xoob/parametric-picture-frame/previews/clips_iso.png

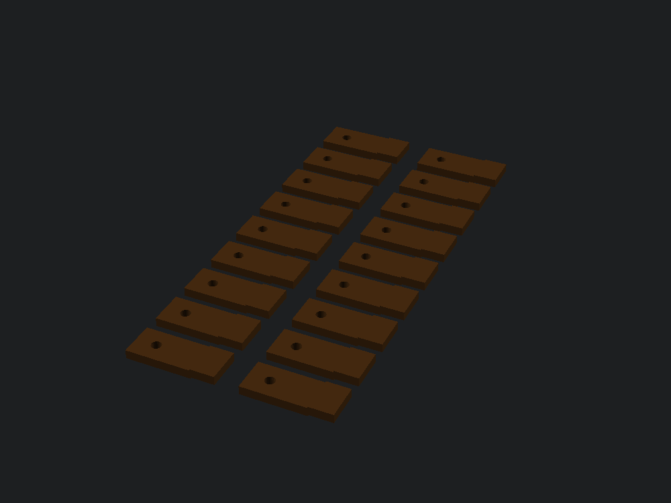
previews/clips_iso.png
