xoob/parametric-picture-frame/previews/f3d_full.png

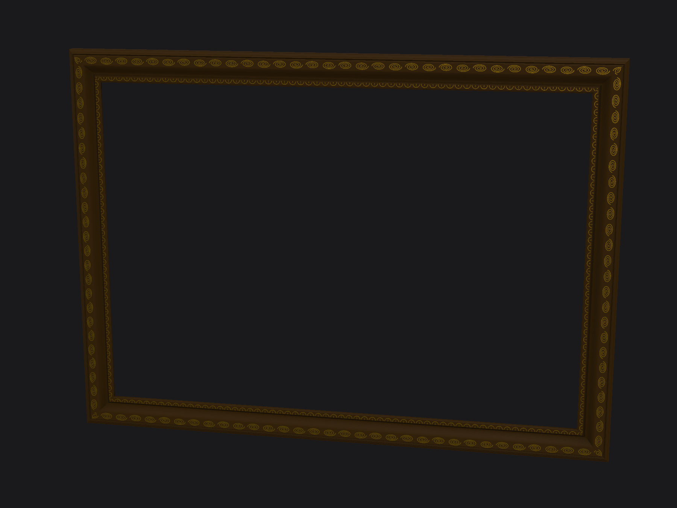
previews/f3d_full.png
