xoob/parametric-picture-frame/previews/fit_iso.png

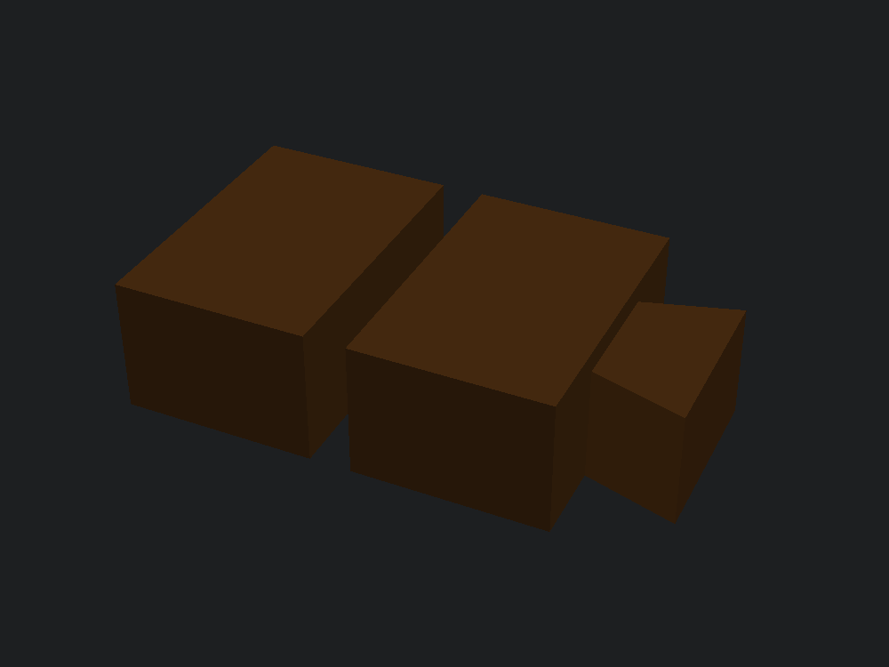
previews/fit_iso.png
