xoob/parametric-picture-frame/previews/hd/clips_iso.png

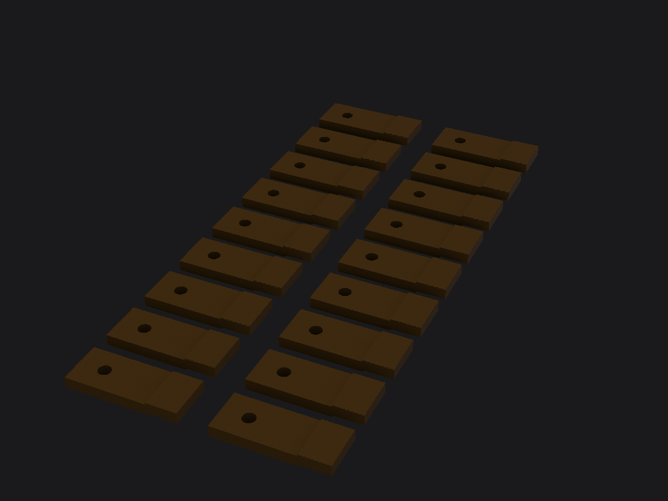
previews/hd/clips_iso.png
