xoob/parametric-picture-frame/previews/hd/corner_bl_back.png

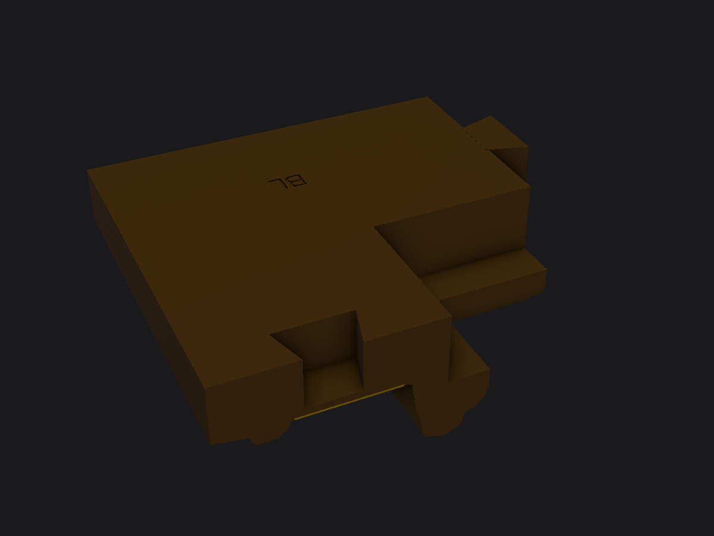
previews/hd/corner_bl_back.png
