xoob/parametric-picture-frame/previews/hd/corner_bl_iso.png

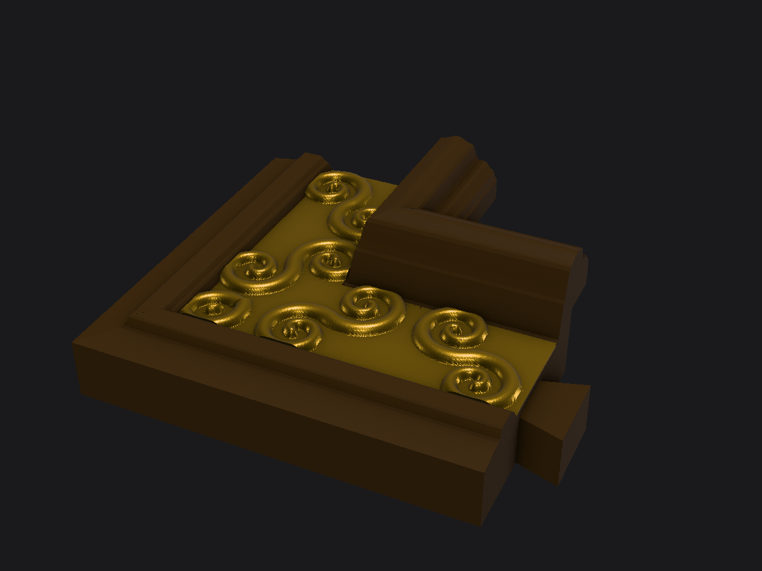
previews/hd/corner_bl_iso.png
