xoob/parametric-picture-frame/previews/hd/exploded_iso.png

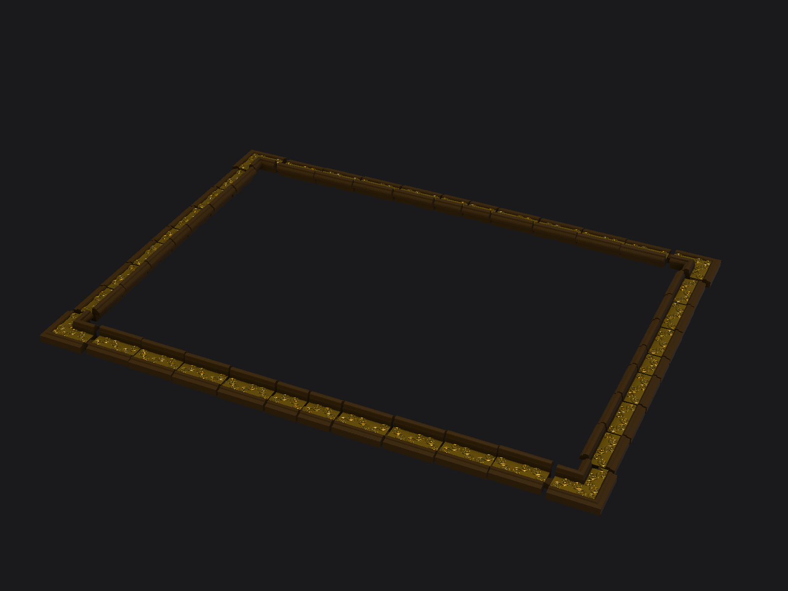
previews/hd/exploded_iso.png
