xoob/parametric-picture-frame/previews/hd/part_b2_iso.png

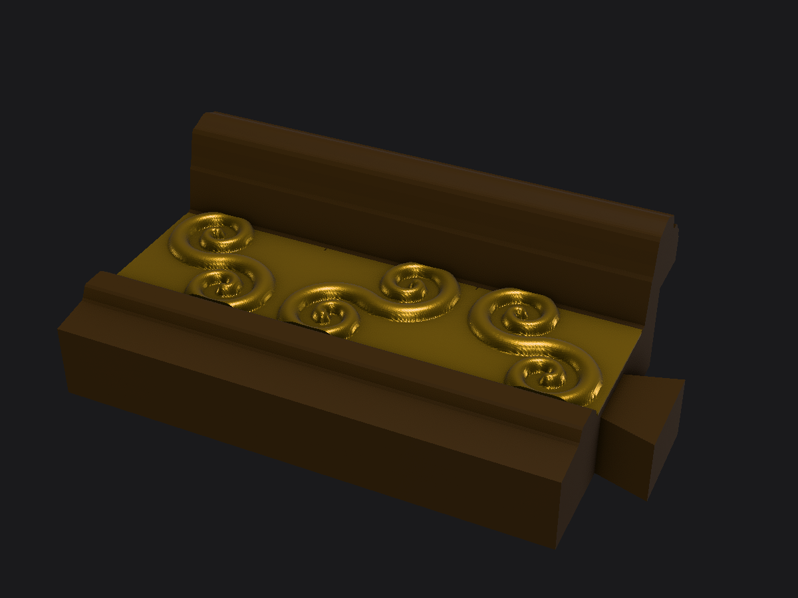
previews/hd/part_b2_iso.png
