xoob/parametric-picture-frame/previews/hd/style_ripple.png

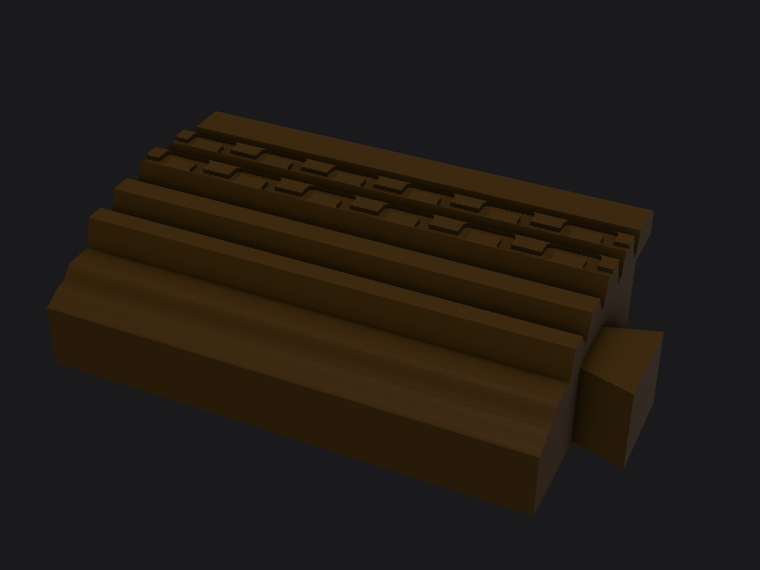
previews/hd/style_ripple.png
