xoob/parametric-picture-frame/previews/part_b2_iso.png

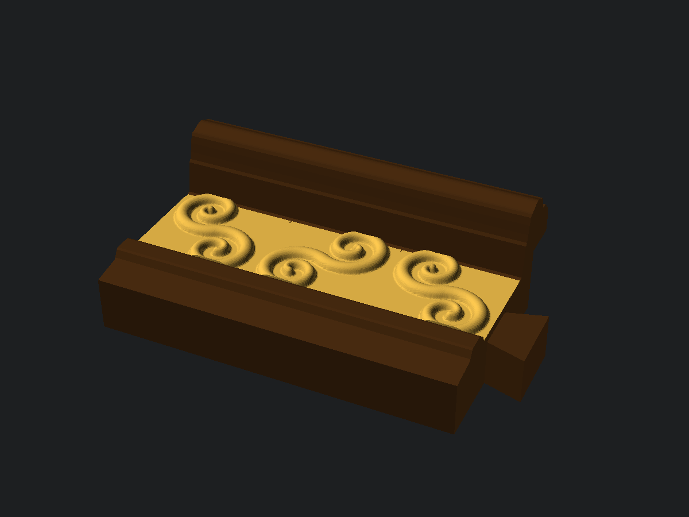
previews/part_b2_iso.png
