xoob/parametric-picture-frame/previews/part_b2_right.png

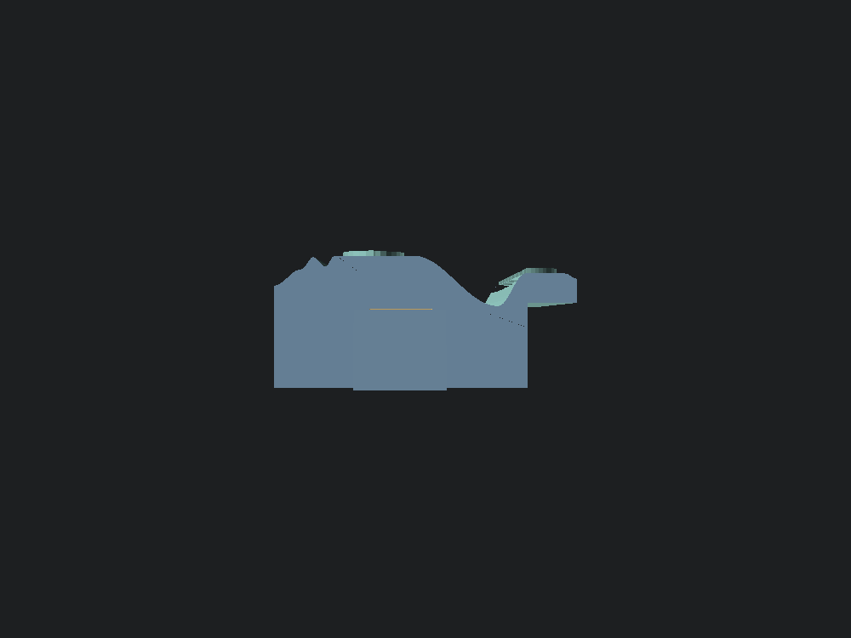
previews/part_b2_right.png
