xoob/parametric-picture-frame/previews/style_revogee.png

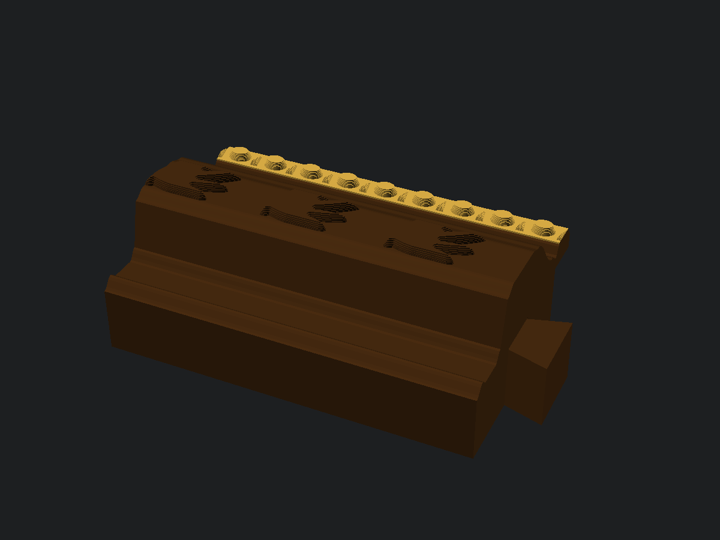
previews/style_revogee.png
