xoob/parametric-picture-frame/previews/assembled_top.png

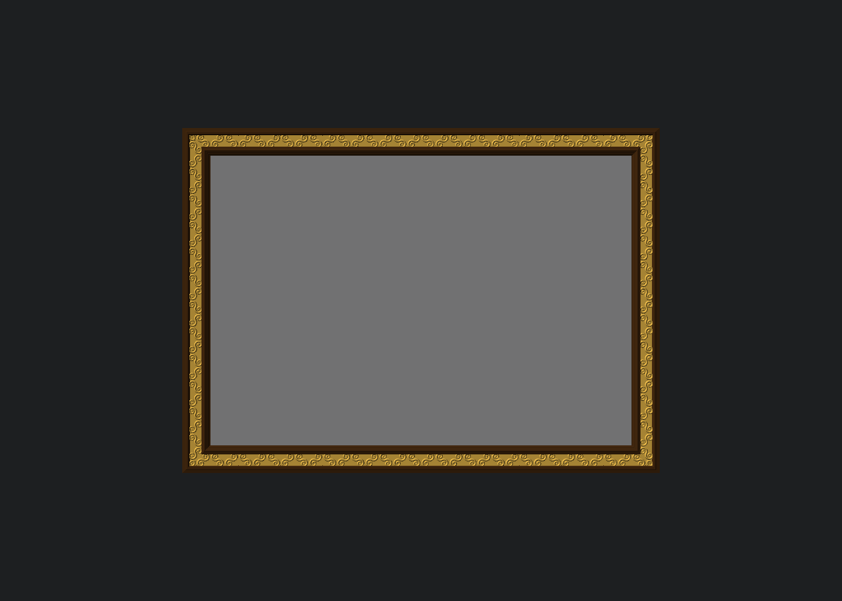
previews/assembled_top.png
