xoob/parametric-picture-frame/previews/hd/assembled_top.png

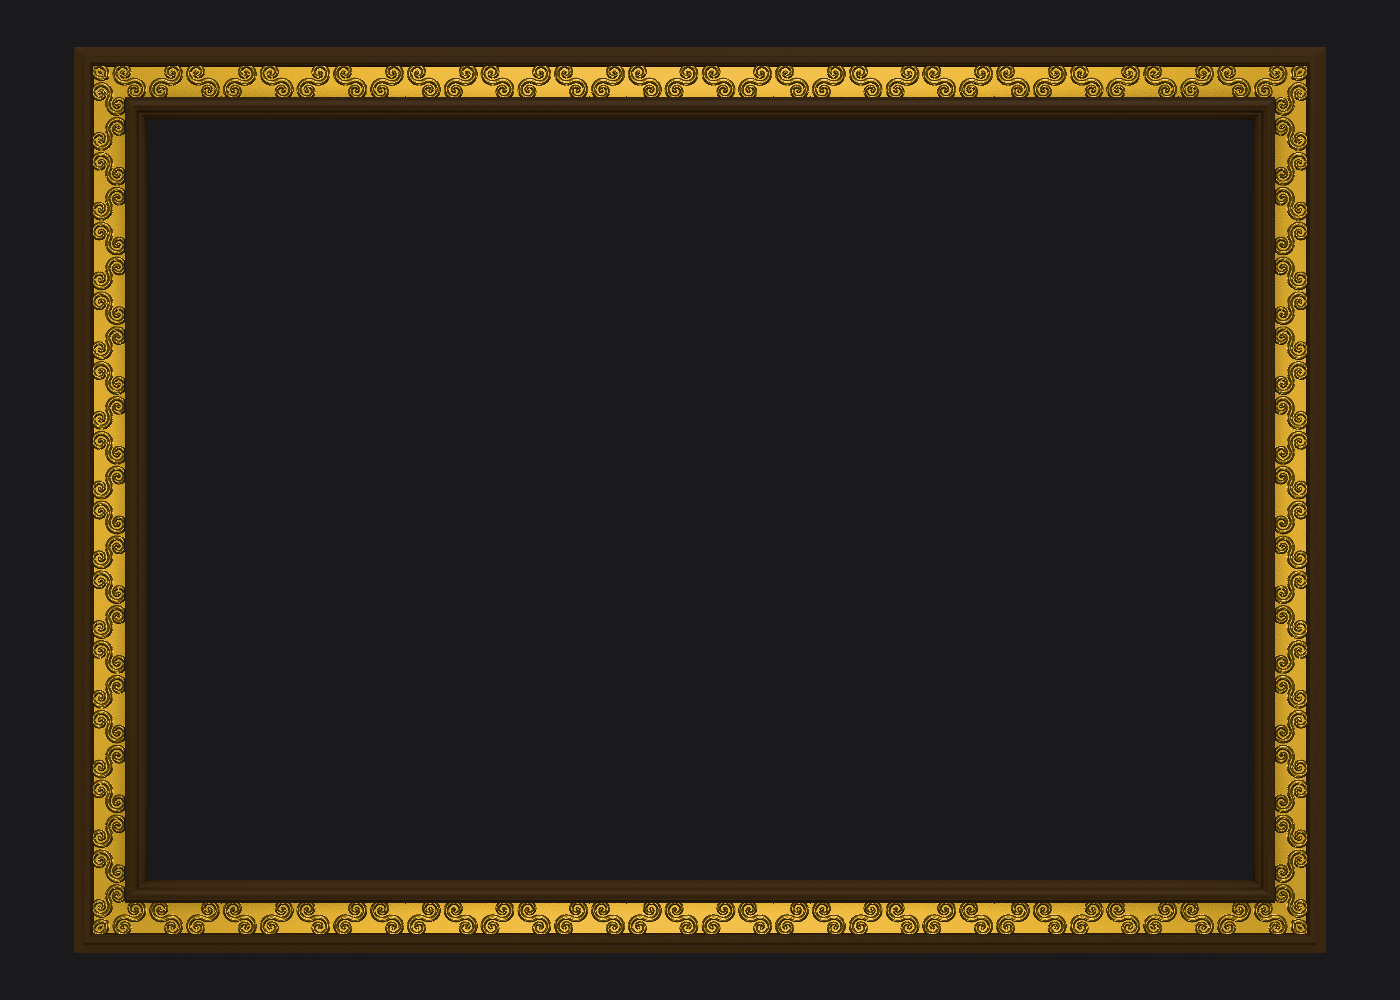
previews/hd/assembled_top.png
